lordofhyphens/E1x/STL Files/Arduino_Flat_Mount.stl

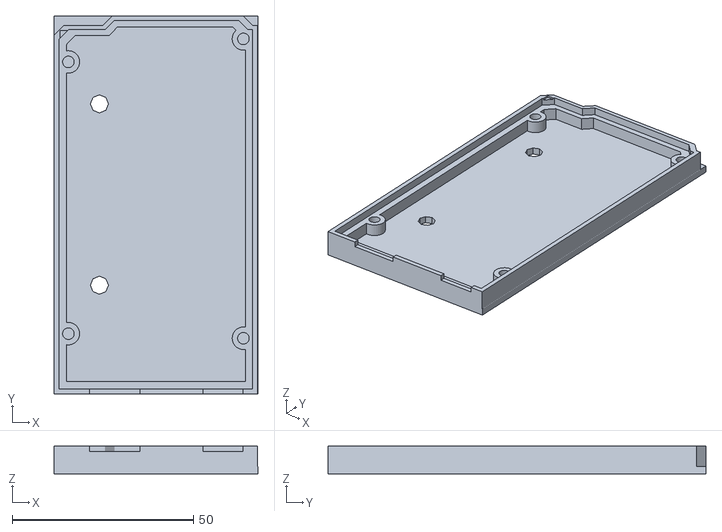
[picture p15: CAD file, 2015-08-30]
STL Files/Arduino_Flat_Mount.stl
56.2 x 104.2 x 7.70
