lordofhyphens/E1x/STL Files/Arduino_Corner_Enclosure.stl

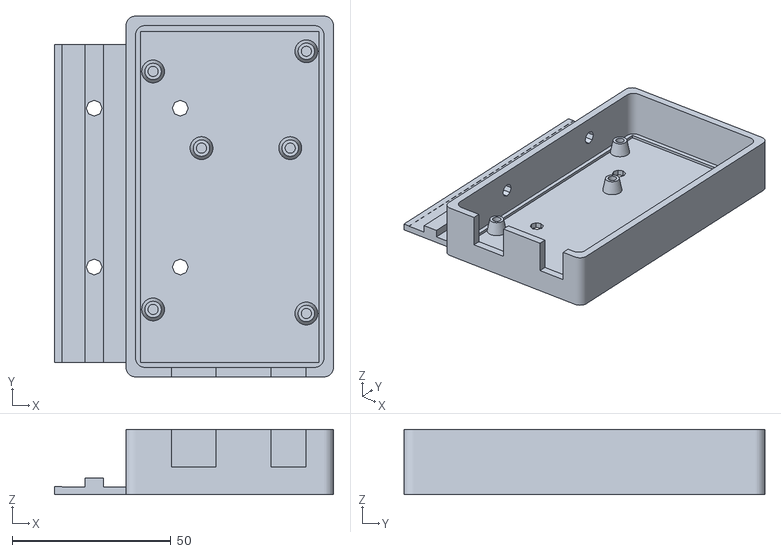
[picture p16: CAD file, 2015-08-30]
STL Files/Arduino_Corner_Enclosure.stl
87.8 x 113.6 x 20.5
