lordofhyphens/E1x/STL Files/Y_Belt_Holder.stl

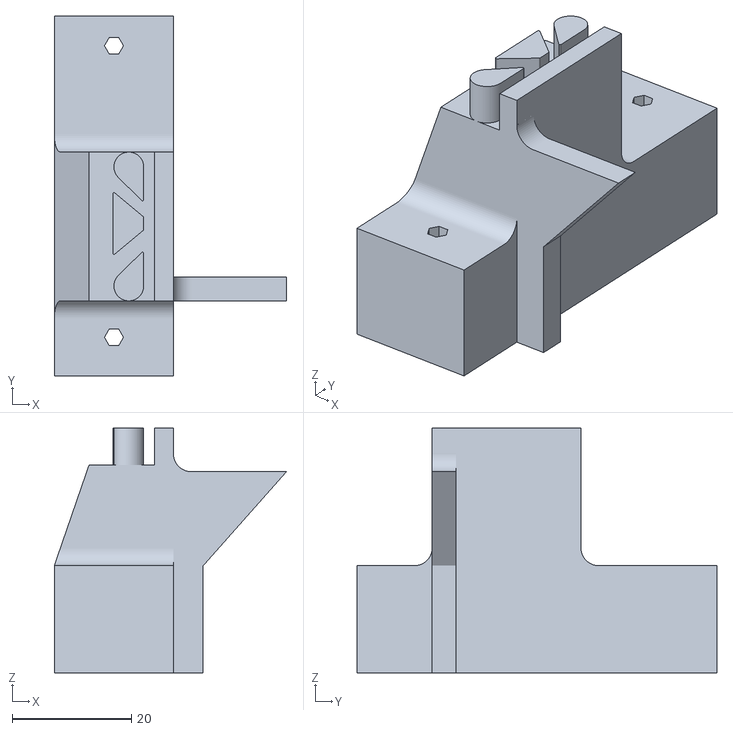
[picture p17: CAD file, 2015-08-30]
STL Files/Y_Belt_Holder.stl
39.0 x 60.5 x 41.1
