lordofhyphens/E1x/STL Files/Arduino_Cornermount.stl

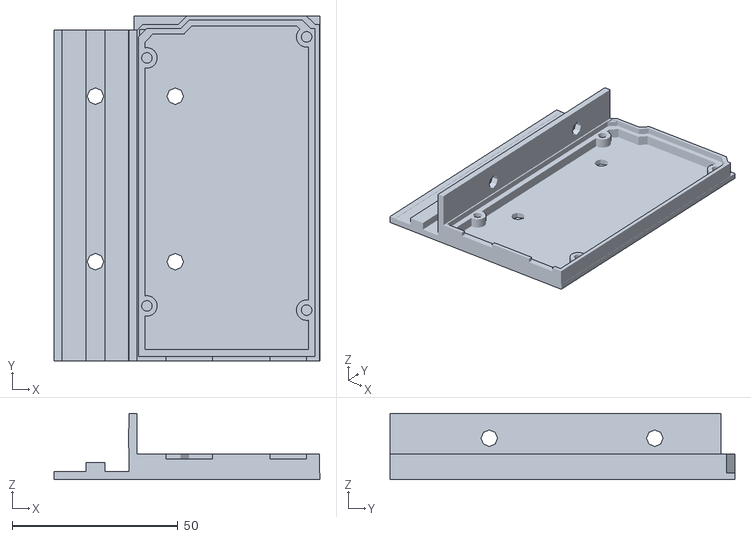
[picture p18: CAD file, 2015-08-30]
STL Files/Arduino_Cornermount.stl
80.3 x 104.2 x 20.0
