lordofhyphens/E1x/STL Files/z_support.stl

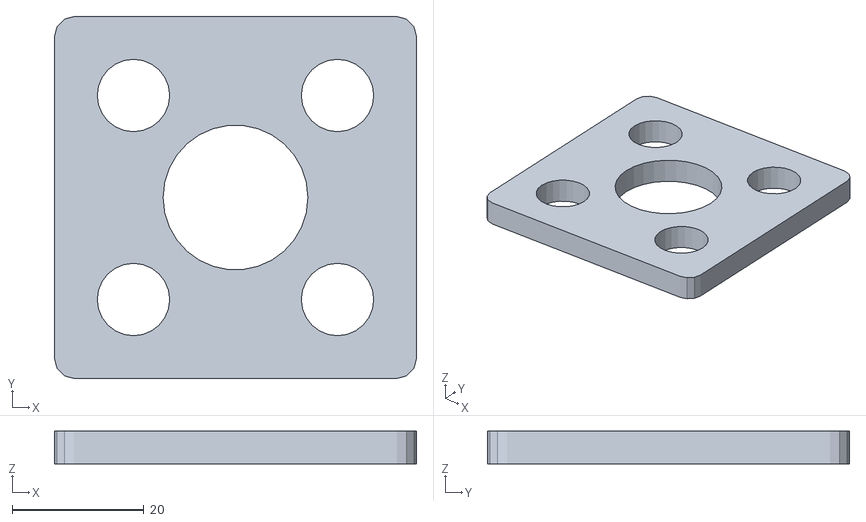
[picture p19: CAD file, 2015-08-30]
STL Files/z_support.stl
55.0 x 55.0 x 5.00
