lordofhyphens/E1x/STL Files/Arduino_Flat_Enclosure.stl

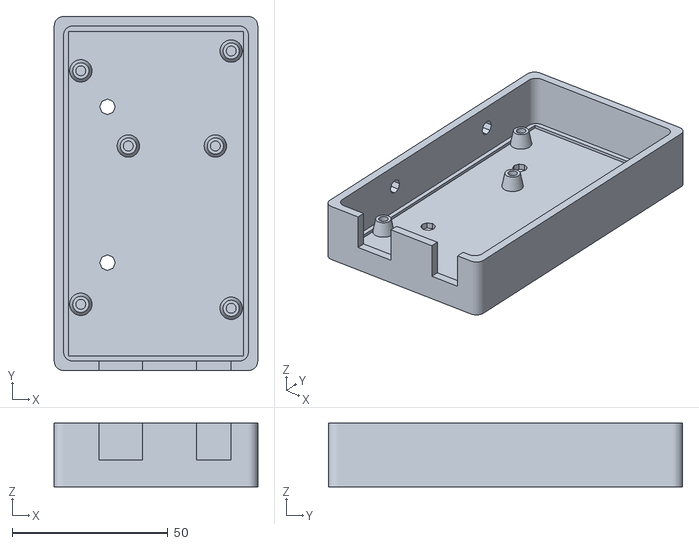
[picture p20: CAD file, 2015-08-30]
STL Files/Arduino_Flat_Enclosure.stl
65.3 x 113.6 x 20.5
