lordofhyphens/E1x/STL Files/M5_Antibacklash_Z_9.5mm_Spring.stl

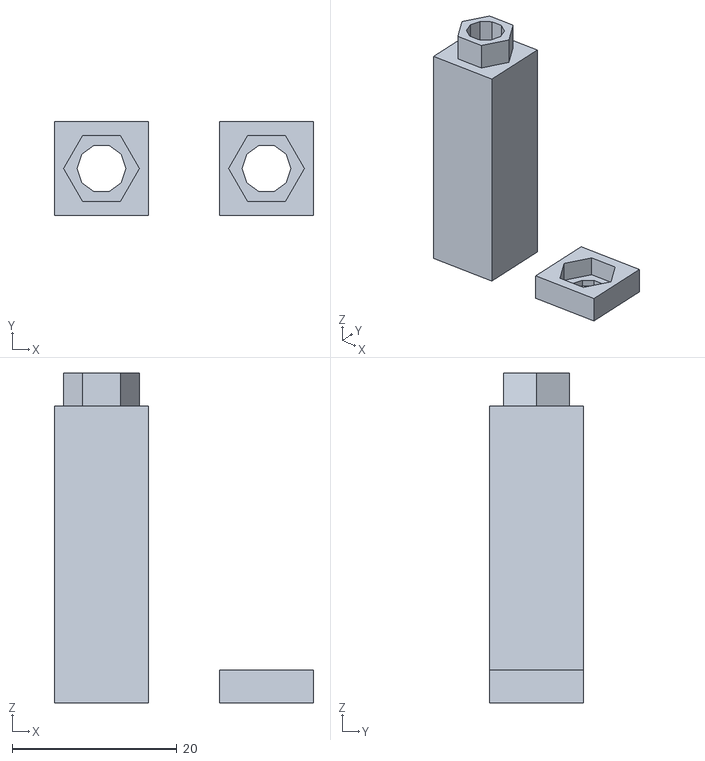
[picture p21: CAD file, 2015-05-23]
STL Files/M5_Antibacklash_Z_9.5mm_Spring.stl
31.4 x 11.4 x 40.0
